The-Wolfson/CableChecker/Firmware/cable-checker/main/gpios.h

//
// Created by Joshua Wolfson on 9/7/2025.
//

#ifndef DEFINITIONS_H
#define DEFINITIONS_H

//GlowBit
#define LED_DIN             39
#define LED_COUNT           8

#define MODE_LED_INDEX      0

//Headphone Jack
#define RSH                 11
#define TSH                 12

//ADA377
#define ROTARY_DT           18
#define ROTARY_CLK          17
#define ROTARY_SW           38

//SP3T
#define SP3T_A              40
#define SP3T_B              41
#define SP3T_C              42

#endif //DEFINITIONS_H
